TheSchilk/SYS_StepAtten/Firmware/Inc/sys_stepatten.h

/*
 * sys_stepatten.h
 *
 *  Created on: 23 Apr 2020
 *      Author: pschilk
 */

#ifndef SYS_STEPATTEN_H_
#define SYS_STEPATTEN_H_

// CMSIS and StdPeriphLib
#include "stm32f0xx.h"


#include "ui.h"
#include "pins.h"
#include "gpio.h"
#include "adc.h"
#include "systick.h"
#include "flash.h"

// The number of inputs
#define INPUT_COUNT 4

#endif /* SYS_STEPATTEN_H_ */
